PricelessToolkit/CapiBridge/img/Nice Images/DSC00671.JPG

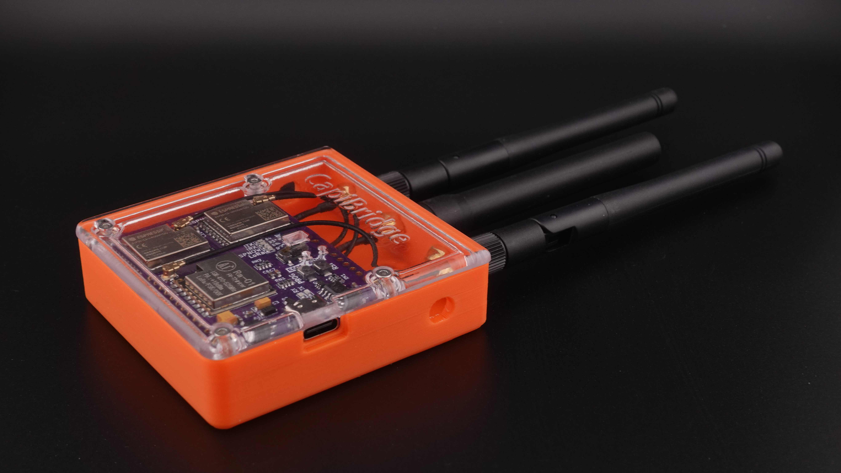
img/Nice Images/DSC00671.JPG
