PricelessToolkit/CapiBridge/img/Nice Images/DSC00677.JPG

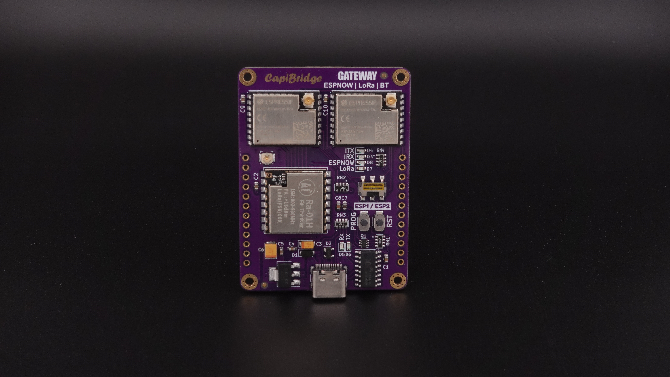
img/Nice Images/DSC00677.JPG
